michaelobed/qad-lights/src/main/main.hpp

//
//  main.hpp
//  qad-lights
//
//  Created by michaelobed on 04/08/2026.
//  
//  Copyright © 2026 Michael Obed.

#ifndef main_hpp
#define main_hpp

#ifndef __cplusplus
extern "C"
{
#endif
    void Restart();

#ifndef __cplusplus
};
#endif

#endif
